Kehaar38/video-sight/docs/ballistics/スクリーンショット 2026-05-29 230836.png

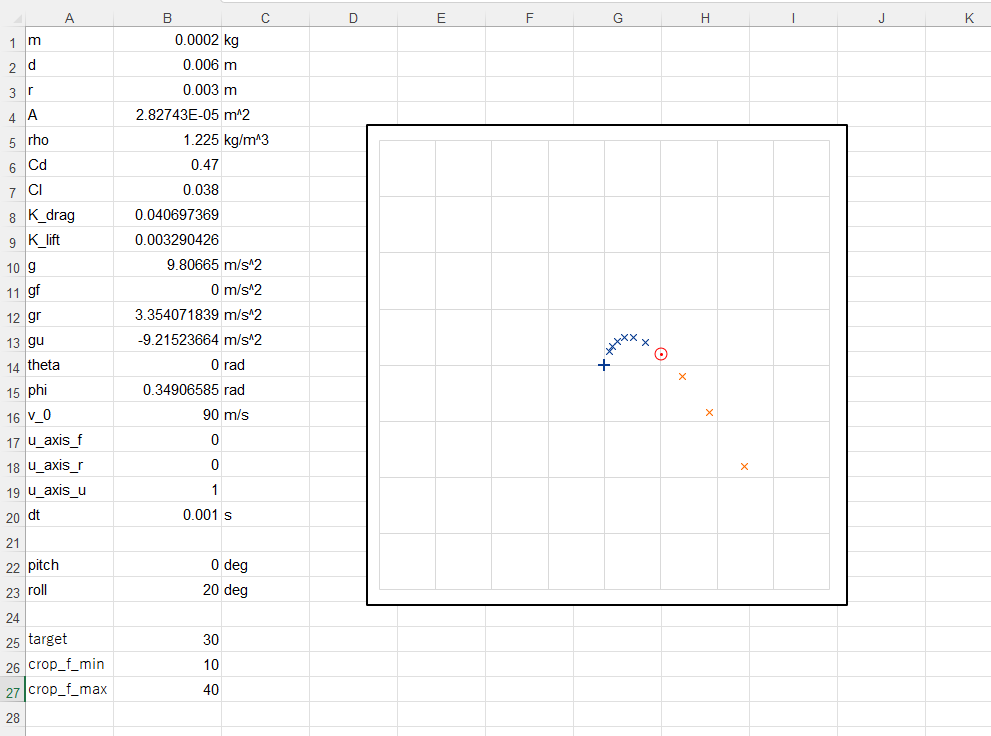
docs/ballistics/スクリーンショット 2026-05-29 230836.png
