Kehaar38/video-sight/hardware/screenshots/20260521/スクリーンショット 2026-05-21 224945.png

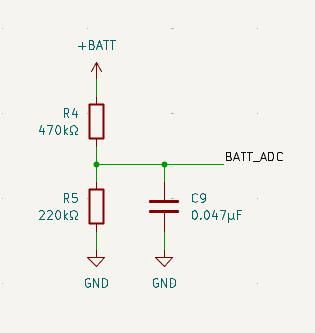
hardware/screenshots/20260521/スクリーンショット 2026-05-21 224945.png
