Kehaar38/video-sight/hardware/screenshots/20260523/スクリーンショット 2026-05-23 180642.png

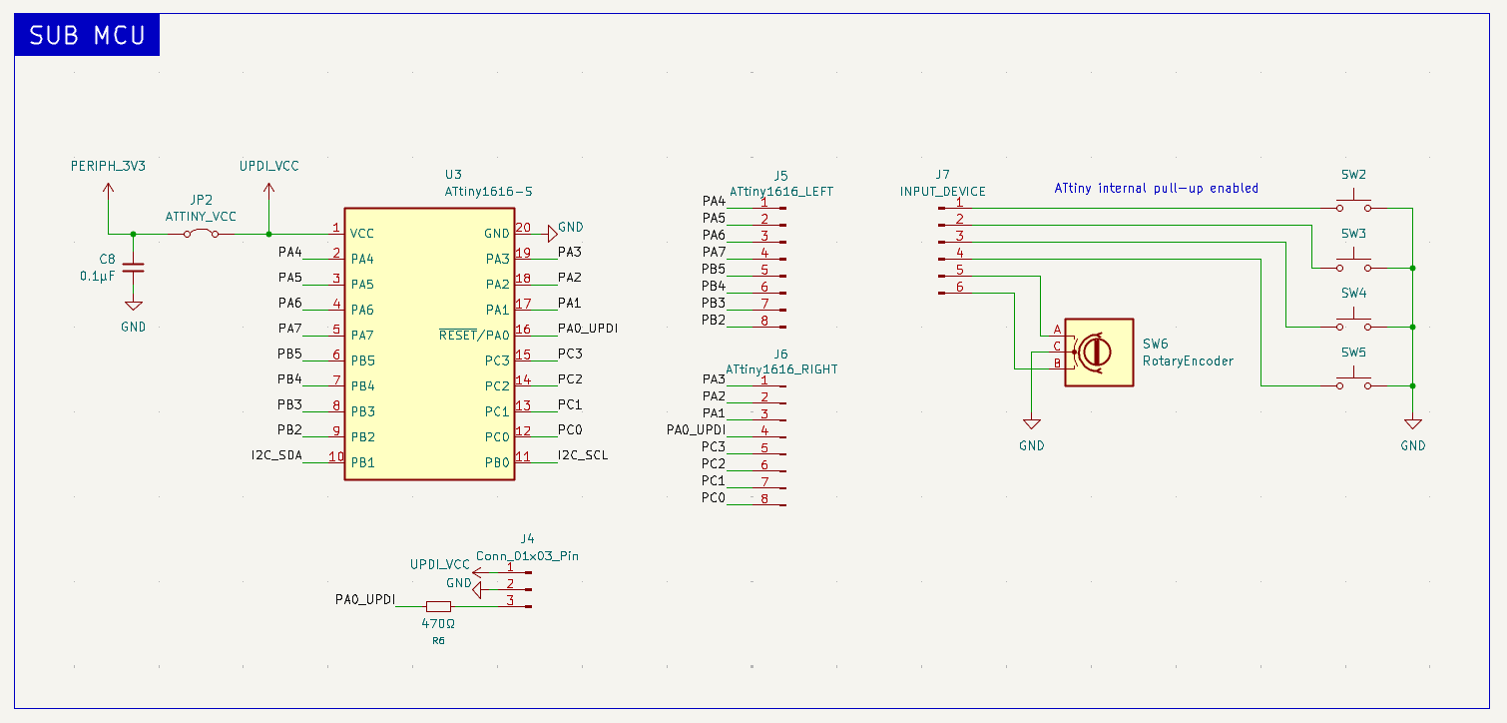
hardware/screenshots/20260523/スクリーンショット 2026-05-23 180642.png
