Kehaar38/video-sight/hardware/screenshots/20260524/スクリーンショット 2026-05-24 230755.png

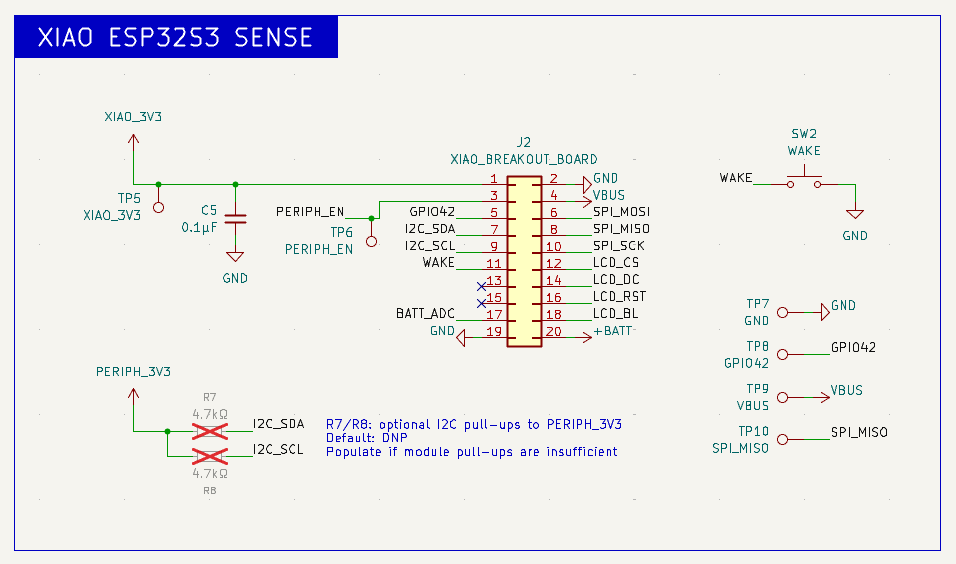
hardware/screenshots/20260524/スクリーンショット 2026-05-24 230755.png
