Kehaar38/video-sight/hardware/screenshots/20260525/スクリーンショット 2026-05-25 234540.png

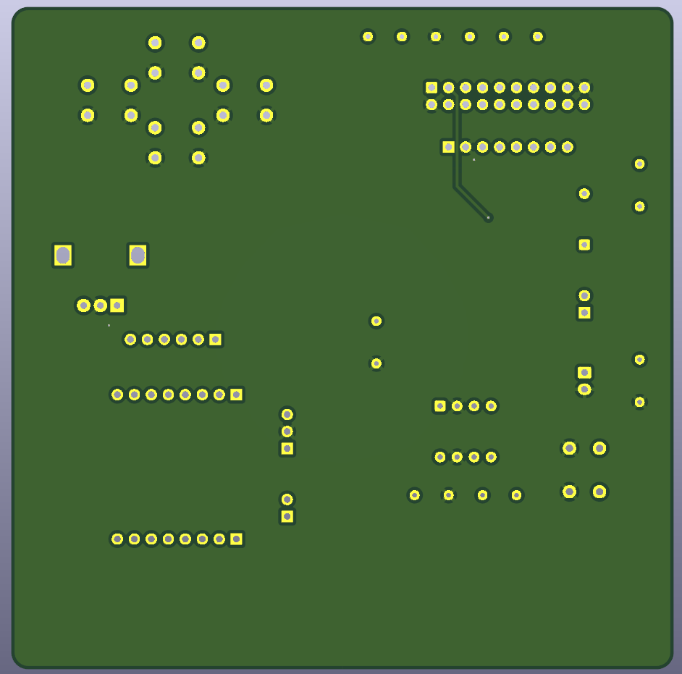
hardware/screenshots/20260525/スクリーンショット 2026-05-25 234540.png
