Kehaar38/video-sight/hardware/screenshots/20260526/スクリーンショット 2026-05-26 223218.png

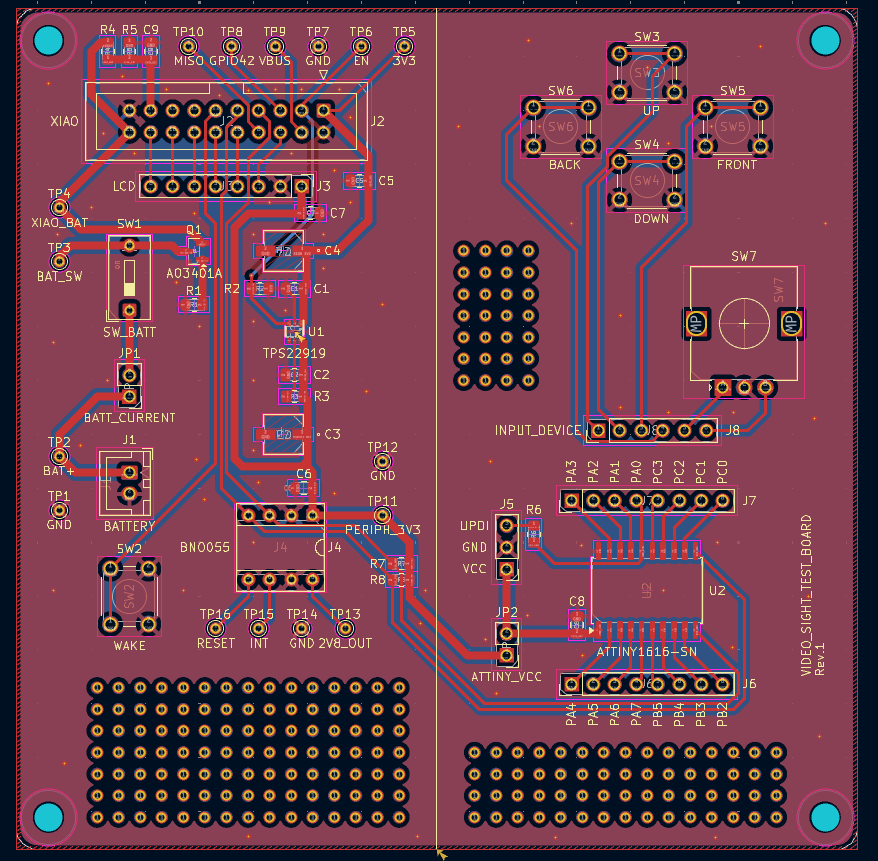
hardware/screenshots/20260526/スクリーンショット 2026-05-26 223218.png
