Kehaar38/video-sight/hardware/screenshots/20260527/スクリーンショット 2026-05-27 230621.png

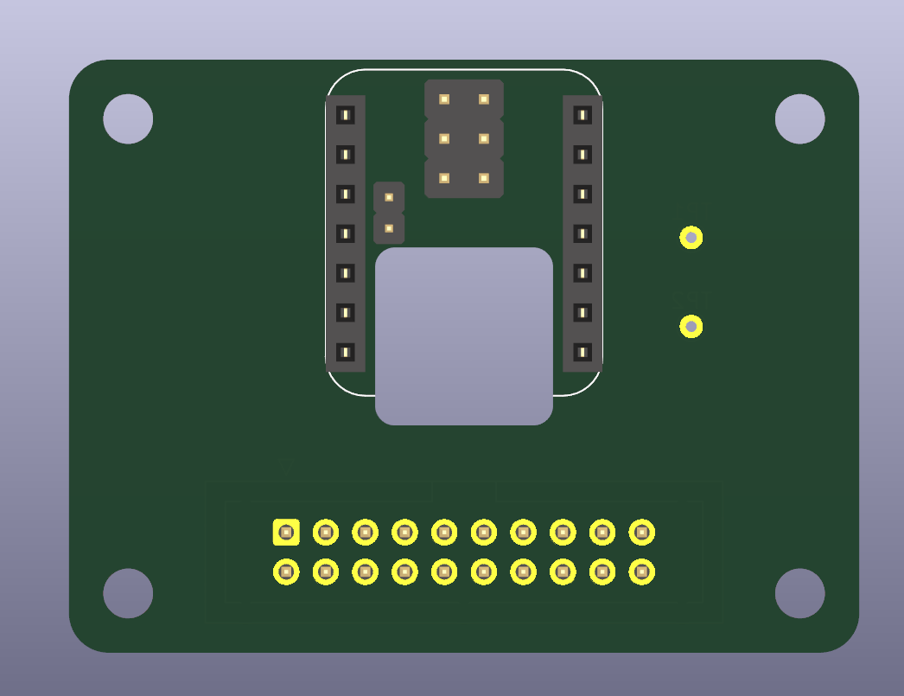
hardware/screenshots/20260527/スクリーンショット 2026-05-27 230621.png
